Uspizig/TinyLoRaEink/2.JPG

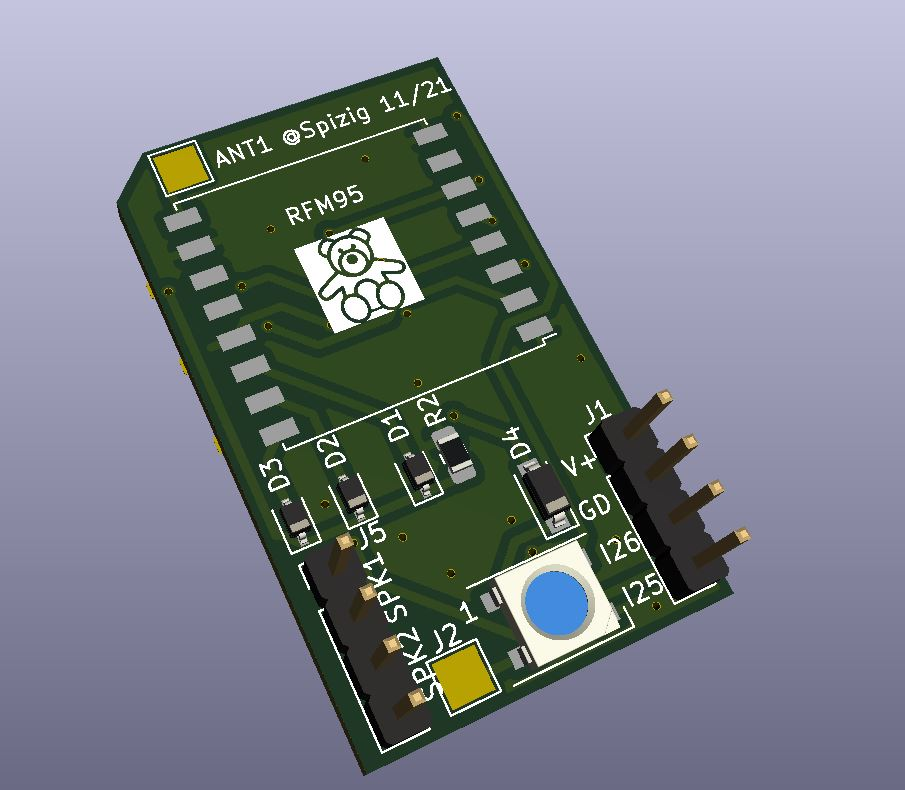
2.JPG
